NorthernWidget-Skunkworks/Project-Okapi/Simulations/LT_ORController.asc

C1: cap; 0.1µF
M1: pmos; FDC638P
M2: pmos; FDC638P
R1: res; 10k
R2: res; 470k
U1: LTC4412
V1: voltage; 3.7
V2: voltage; PULSE(0 5 1e-3 1e-9 1e-9 2e-3 4e-3 2)
Named nets: 0
.tran 5e-3
