NorthernWidget-Skunkworks/Project-Okapi/Particle_Files/Boron_Serial_Dummy.ino

SYSTEM_MODE(MANUAL);

void setup() {
    Serial.begin(9600);
    pinMode(D4, INPUT);
    delay(3000);
    pinMode(D4, OUTPUT);
}

void loop() {
    Serial.println("BANG");
    digitalWrite(D4, HIGH);
    delay(1000);
    digitalWrite(D4, LOW);
    delay(1000);
}
